Wbiu/WVR-Glove-Wiki/Glove_STL/servo holders/Servo holder left and thunmb half.stl

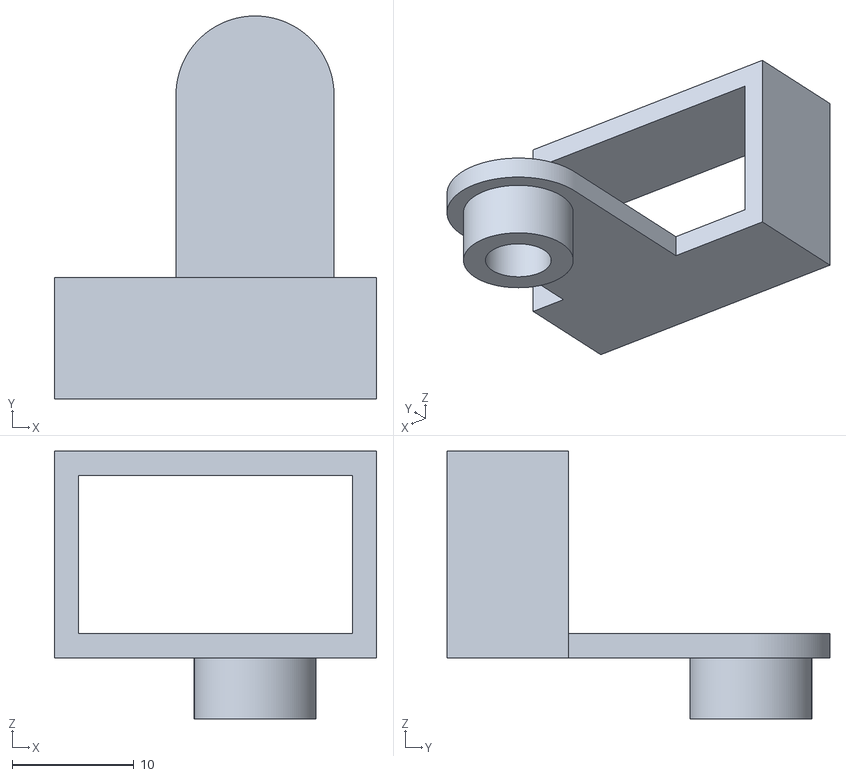
[picture p16: CAD file, 2023-03-25]
Glove_STL/servo holders/Servo holder left and thunmb half.stl
26.5 x 31.5 x 22.0
