Wbiu/WVR-Glove-Wiki/Glove_STL/finger tips size/index and ring/Index-Ring Tip_L.stl

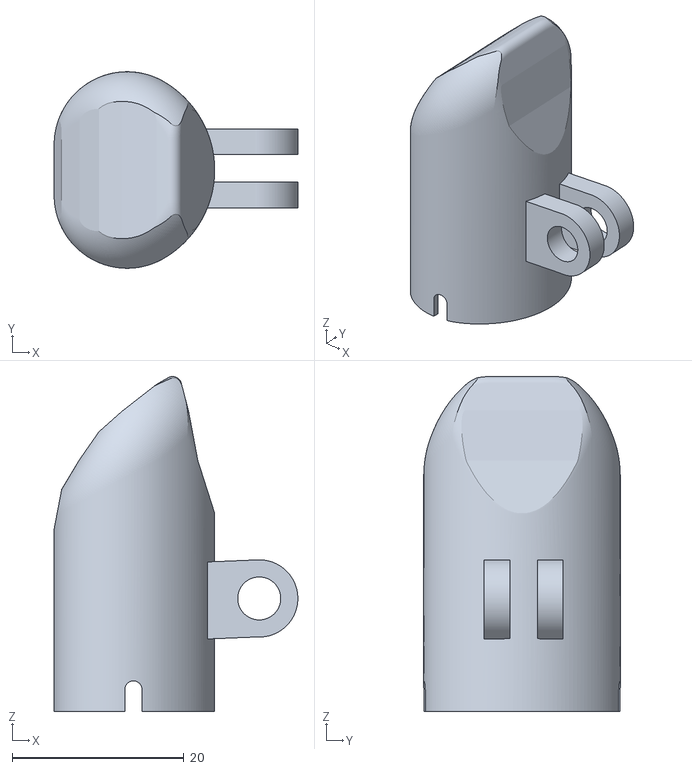
[picture p17: CAD file, 2023-03-25]
Glove_STL/finger tips size/index and ring/Index-Ring Tip_L.stl
28.4 x 22.9 x 39.0
