Wbiu/WVR-Glove-Wiki/Glove_STL/finger tips size/pinky/Pinky Tip_M.stl

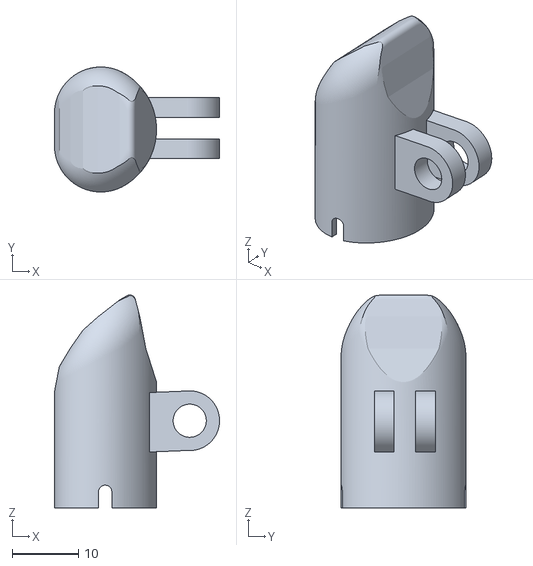
[picture p18: CAD file, 2023-03-25]
Glove_STL/finger tips size/pinky/Pinky Tip_M.stl
24.9 x 18.8 x 32.1
