Wbiu/WVR-Glove-Wiki/Glove_STL/finger tips size/thumb/Thumb Tip_L.stl

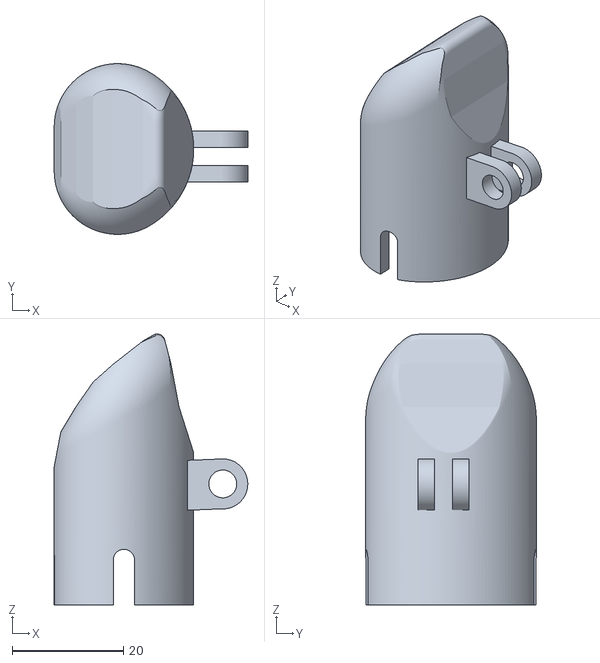
[picture p19: CAD file, 2023-03-25]
Glove_STL/finger tips size/thumb/Thumb Tip_L.stl
34.8 x 30.7 x 48.7
