Wbiu/WVR-Glove-Wiki/Glove_STL/Handcover Top.stl

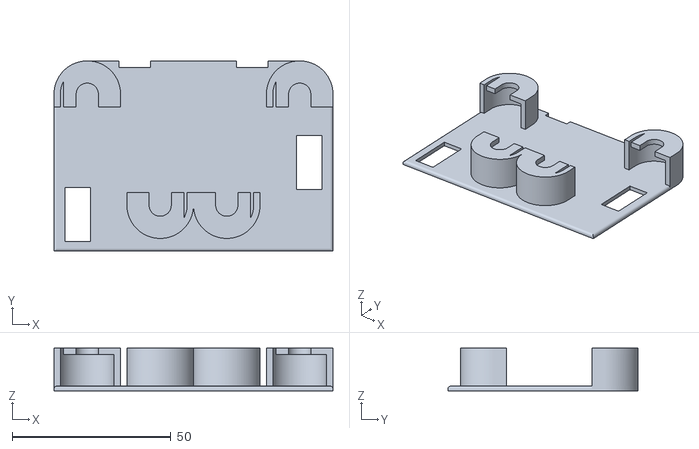
[picture p20: CAD file, 2023-03-25]
Glove_STL/Handcover Top.stl
88.0 x 60.0 x 13.5
