Wbiu/WVR-Glove-Wiki/Glove_STL/servo arms/Servo arm thumb.stl

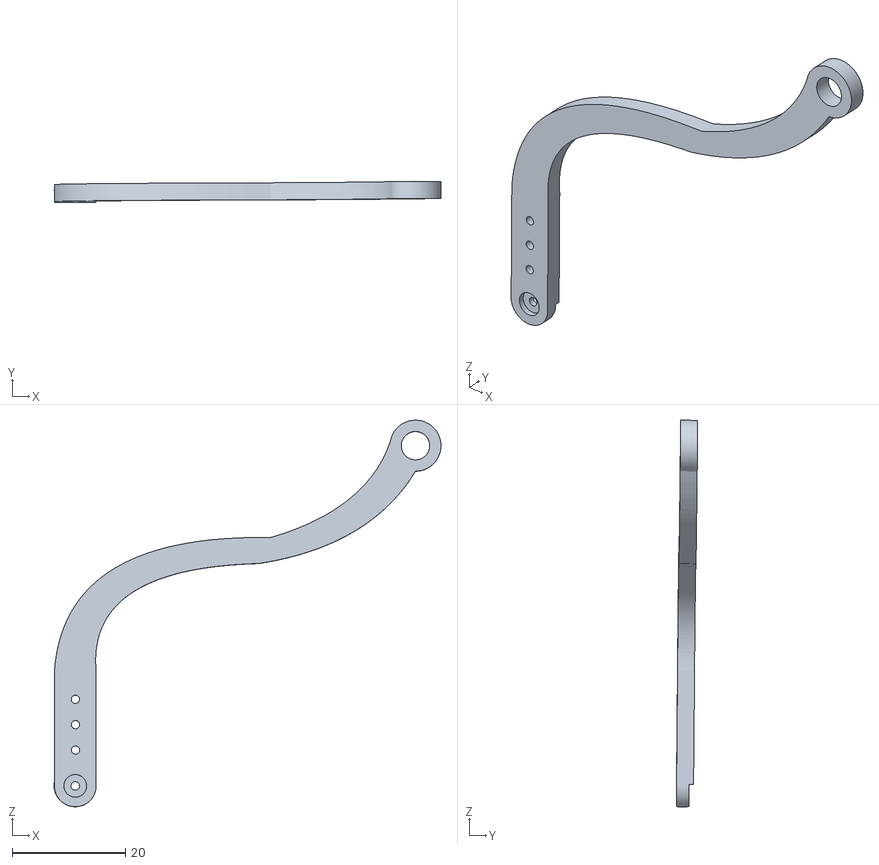
[picture p21: CAD file, 2023-03-25]
Glove_STL/servo arms/Servo arm thumb.stl
68.3 x 3.76 x 68.2
