Wbiu/WVR-Glove-Wiki/Glove_STL/Thumb holder amb.stl

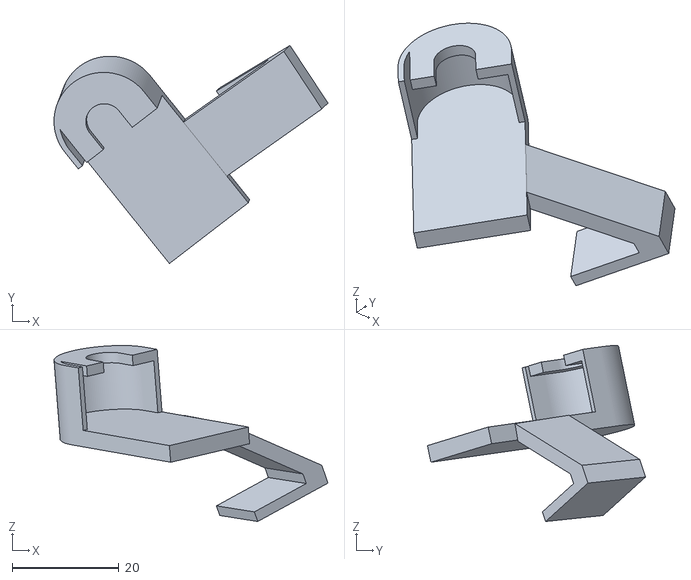
[picture p22: CAD file, 2023-03-25]
Glove_STL/Thumb holder amb.stl
51.4 x 40.9 x 33.0
